juwis/SolarStuff/src/autompptbldc/autompptbldc/includes.h

/*
 * includes.h
 *
 * Created: 14.11.2018 16:45:53
 *  Author: JWingert
 */ 


#ifndef INCLUDES_H_
#define INCLUDES_H_

#define F_CPU 32000000UL
#include <avr/interrupt.h>
#include <util/delay.h>
#include <stdio.h>
#include <avr/io.h>

#endif /* INCLUDES_H_ */
