juwis/SolarStuff/atmel_flip_modified/common.services.usb.class.dfu_atmel.device.bootloader.atxmega16a4u/common/services/usb/class/dfu_flip/device/bootloader/xmega/conf/conf_isp.h

/**
 * \file
 *
 * \brief ISP configuration file.
 *
 * Copyright (c) 2011-2012 Atmel Corporation. All rights reserved.
 *
 * \asf_license_start
 *
 * \page License
 *
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
 * 3. The name of Atmel may not be used to endorse or promote products derived
 *    from this software without specific prior written permission.
 *
 * 4. This software may only be redistributed and used in connection with an
 *    Atmel microcontroller product.
 *
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
 * \asf_license_stop
 *
 */

#ifndef _CONF_ISP_H_
#define _CONF_ISP_H_

#include "parts.h"

#if !defined(__ASSEMBLER__) && !defined(__IAR_SYSTEMS_ASM__)
// This define may only be included from C files

#include "compiler.h"
#include "nvm.h"


// Bootloader Versions
// Example: Version 0x00 give 1.0.0 on batchisp log
// Example: Version 0x03 give 1.0.3 on batchisp log
// Example: Version 0x25 give 1.2.5 on batchisp log
#  define BOOTLOADER_VERSION   0x04

#  if (FLASH_SIZE<=0x10000) // FLASH <= 64KB
// If all memories (flash,eeprom,...) do not exceed 64KB.
// then the ISP interface can be optimized to save CODE.
#    define ISP_SMALL_MEMORY_SIZE
#  endif

#endif

// Definition of hardware condition to enter in ISP mode
//Changed this!
//to fit the mppt bldc enable pin
# define ISP_PORT_DIR      PORTE_DIR
# define ISP_PORT_PINCTRL  PORTE_PIN3CTRL
# define ISP_PORT_IN       PORTE_IN
# define ISP_PORT_PIN      3

#endif // _CONF_ISP_H_
